jagould2012/cyberdeck/images/power_drawing.png

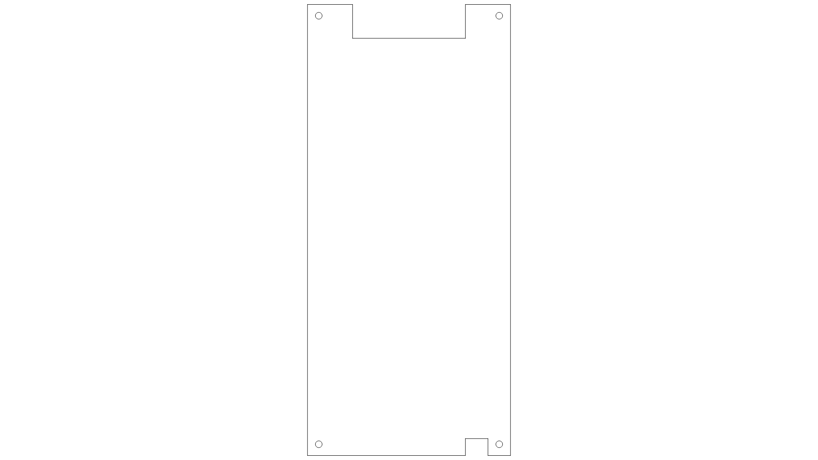
images/power_drawing.png
